juanmitaboada/fitebox/doc/big/img_off.png

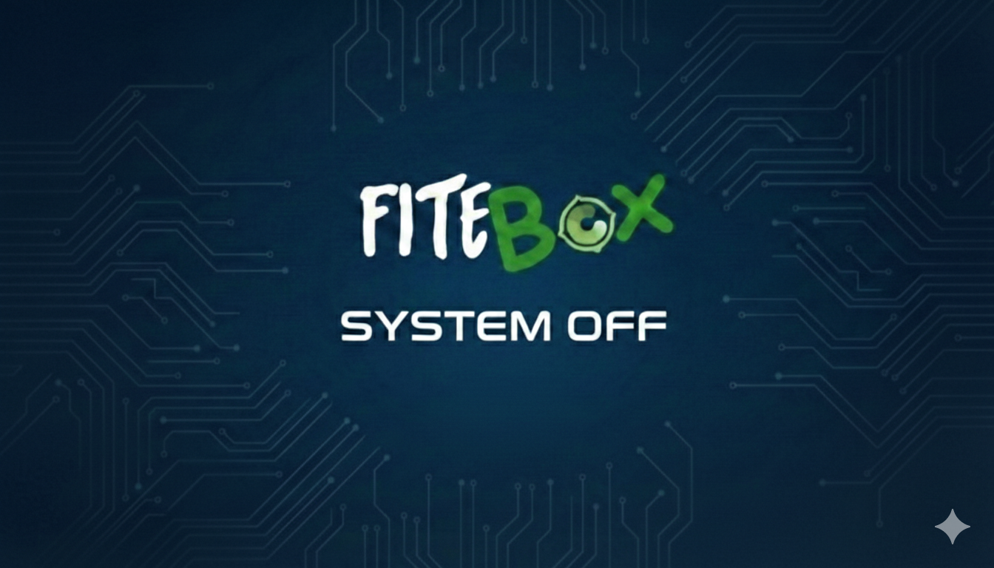
doc/big/img_off.png
