juanmitaboada/fitebox/doc/media/background26.png

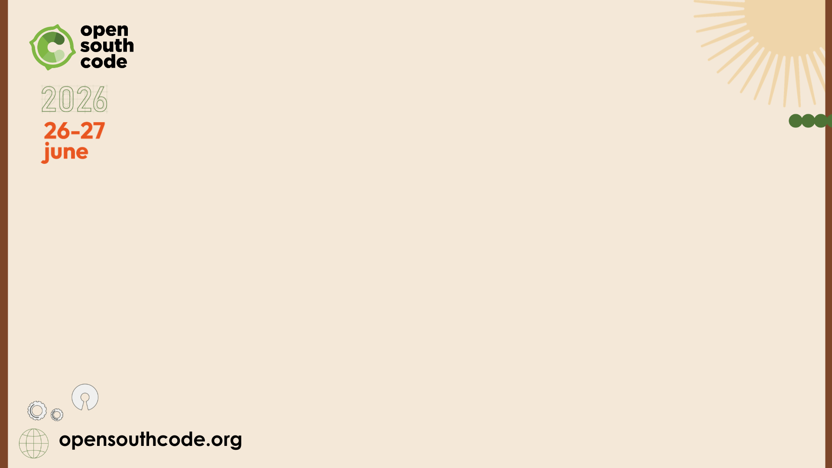
doc/media/background26.png
